waagbo/picogus/sw/system/flash_settings.c

/*
 *  Copyright (C) 2022-2024  Ian Scott
 *
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
 *  You should have received a copy of the GNU General Public License along
 *  with this program; if not, write to the Free Software Foundation, Inc.,
 *  51 Franklin Street, Fifth Floor, Boston, MA 02110-1301, USA.
 */

#include <string.h>

#include "flash_settings.h"
#include "../../common/picogus.h"   // DFS_DEFAULT_DATA_PORT
#include "../include/pg_debug.h"
#include "overclock.h"
#include "hardware/flash.h"
#include "hardware/sync.h"
#include "hardware/clocks.h"
#include "pico/stdlib.h"

static const Settings defaultSettings = {
    .magic = SETTINGS_MAGIC,
    .version = SETTINGS_VERSION,
    .startupMode = 1,
    .Global = {
        .waveTableVolume = 100
    },
    .Joy = {
        .basePort = 0xffff
    },
    .GUS = {
        .basePort = 0x240,
        .audioBuffer = 4,
        .dmaInterval = 0,
        .force44k = false
    },
    .SB = {
        .basePort = 0x220,
        .oplBasePort = 0x388,
        .oplSpeedSensitive = false
    },
    .MPU = {
        .basePort = 0x330,
        .delaySysex = false,
        .fakeAllNotesOff = false
    },
    .CMS = {
        .basePort = 0x220
    },
    .Tandy = {
        .basePort = 0x2c0
    },
    .Mouse = {
        .basePort = 0xffff,
        .protocol = 0,
        .reportRate = 60,
        .sensitivity = 0x100
    },
    .NE2K = {
        .basePort = 0x300,
    },
    .WiFi = {
        .ssid = {0},
        .password = {0}
    },
    .CD = {
        .basePort = 0x250,
        .autoAdvance = true
    },
    .MMB = {
        // Mindscape Music Board defaults to off because its port is so common
        .basePort = 0xffff
    },
    .Volume = {
        .mainVol = 100,
        .oplVol = 100,
        .sbVol = 90,
        .cdVol = 100,
        .gusVol = 100,
        .psgVol = 80
    },
    .SB16 = {
        .irq = 5,
        .dma = 1,
        .sbType = 6,
        .fixTC = 0,
        .lockMixer = 0
    },
    .DFS = {
        .basePort = DFS_DEFAULT_DATA_PORT
    },
    .BootDisk = {
        .fdImage = {0},
        .hdImage = {0},
        .options = 0
    }
};


#define SETTINGS_SECTOR (PICO_FLASH_SIZE_BYTES - FLASH_SECTOR_SIZE)   //  last sector of a 2M flash (adjust for other flash sizes if needed)

typedef struct {
    size_t offset;  // Offset of field in Settings struct
    size_t size;    // Size of field
} FieldInfo;

typedef struct {
    const FieldInfo* fields;
    size_t count;
} VersionFields;

#define FIELD(name) {offsetof(Settings, name), sizeof(((Settings*)0)->name)}

// table of fields added in each version
// when adding new fields, add them to the appropriate version entry
// index corresponds to version number (index 0 = version 1, etc.)
static const VersionFields versionFieldsTable[] = {
    // version 1
    {NULL, 0},

    // version 2 - added NE2K and WiFi settings
    {(const FieldInfo[]){
        FIELD(NE2K),
        FIELD(WiFi),
    }, 2},

    // version 3 - added CD and MMB settings
    {(const FieldInfo[]){
        FIELD(CD),
        FIELD(MMB),
    }, 2},

    // version 4 - added Volume settings
    {(const FieldInfo[]){
        FIELD(Volume),
    }, 1},

    // version 5 - added SB16 settings
    {(const FieldInfo[]){
        FIELD(SB16),
    }, 1},

    // version 6 - added PGDFS settings
    {(const FieldInfo[]){
        FIELD(DFS),
    }, 1},

    // version 7 - added PGBOOT settings (disk image names and options)
    {(const FieldInfo[]){
        FIELD(BootDisk),
    }, 1},
};

// Apply default values only to fields introduced after the given version
static void migrateSettings(Settings* settings, uint8_t oldVersion) {
    // Start with the current settings (preserves old values)
    // Then selectively copy new fields from defaults

    // Apply defaults for all versions newer than oldVersion
    for (uint8_t v = oldVersion + 1; v <= SETTINGS_VERSION; v++) {
        size_t versionIndex = v - 1;

        if (versionIndex >= sizeof(versionFieldsTable) / sizeof(VersionFields)) {
            break;
        }

        const VersionFields* vf = &versionFieldsTable[versionIndex];
        if (vf->fields == NULL || vf->count == 0) {
            continue;
        }

        // Copy each new field from defaults
        for (size_t i = 0; i < vf->count; i++) {
            memcpy((uint8_t*)settings + vf->fields[i].offset,
                   (uint8_t*)&defaultSettings + vf->fields[i].offset,
                   vf->fields[i].size);
        }
    }

    // Update version to current
    settings->version = SETTINGS_VERSION;
}

void loadSettings(Settings* settings, bool migrate)
{
    DBG_PRINTF("copying settings to %u from %u with size %u\n", settings, XIP_BASE + SETTINGS_SECTOR, sizeof(Settings));
    memcpy(settings, (void *)(XIP_BASE + SETTINGS_SECTOR), sizeof(Settings));
    /* stdio_flush(); */

    if (settings->magic != SETTINGS_MAGIC || settings->version > SETTINGS_VERSION) {
        // No valid settings found, use defaults
        DBG_PUTS("No valid settings found, using defaults");
        stdio_flush();
        memcpy(settings, &defaultSettings, sizeof(Settings));
        return;
    }

    if (migrate && settings->version < SETTINGS_VERSION) {
        // Older version found - preserve existing fields, apply defaults to new ones
        DBG_PRINTF("Migrating settings from version %d to %d\n", settings->version, SETTINGS_VERSION);
        stdio_flush();
        migrateSettings(settings, settings->version);
    }

    stdio_flush();
}


// Settings are programmed as whole flash pages; since version 7 (PGBOOT image
// names) they take two. Older firmware reads only the first page's worth.
#define SETTINGS_FLASH_BYTES (((sizeof(Settings) + FLASH_PAGE_SIZE - 1) / FLASH_PAGE_SIZE) * FLASH_PAGE_SIZE)
static_assert(SETTINGS_FLASH_BYTES <= FLASH_SECTOR_SIZE, "Settings struct doesn't fit inside the settings flash sector");
static_assert(sizeof(versionFieldsTable) / sizeof(VersionFields) == SETTINGS_VERSION,
              "versionFieldsTable needs one entry per settings version");

void saveSettings(const Settings* settings)
{
    static uint8_t data[SETTINGS_FLASH_BYTES];  // static: this runs on the small core 0 stack
    memset(data, 0, sizeof(data));
    memcpy(data, settings, sizeof(Settings));
    DBG_PRINTF("doing settings save: ");
    // No need for flash_safe_execute or stop second core, since it will not touch flash
    // If the 2nd core will ever touch flash, reconsider this approach!
    // Clock down the RP2040 so the flash at its default 1/2 clock divider is within spec (<=133MHz)
    set_sys_clock_khz(240000, true);

    DBG_PUTCHAR('/');
    uint32_t ints = save_and_disable_interrupts();
    flash_range_erase(SETTINGS_SECTOR, FLASH_SECTOR_SIZE);    // last sector
    DBG_PUTCHAR('/');
    flash_range_program(SETTINGS_SECTOR, data, SETTINGS_FLASH_BYTES);
    restore_interrupts(ints);
    overclock_370mhz();
    DBG_PRINTF("settings saved");
}

void getDefaultSettings(Settings* settings)
{
    memcpy(settings, &defaultSettings, sizeof(Settings));
}
